jonthomasson/POVSpinner/rev1.c/board_outline/outline5b.dxf

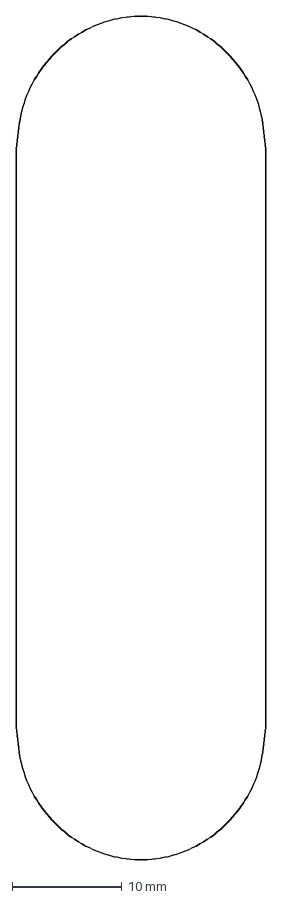
[picture p19: CAD file, 2017-06-09]
rev1.c/board_outline/outline5b.dxf
22.7 x 76.8 mm
