jonthomasson/POVSpinner/rev1.f/3dmodels/Bearings_R188.step

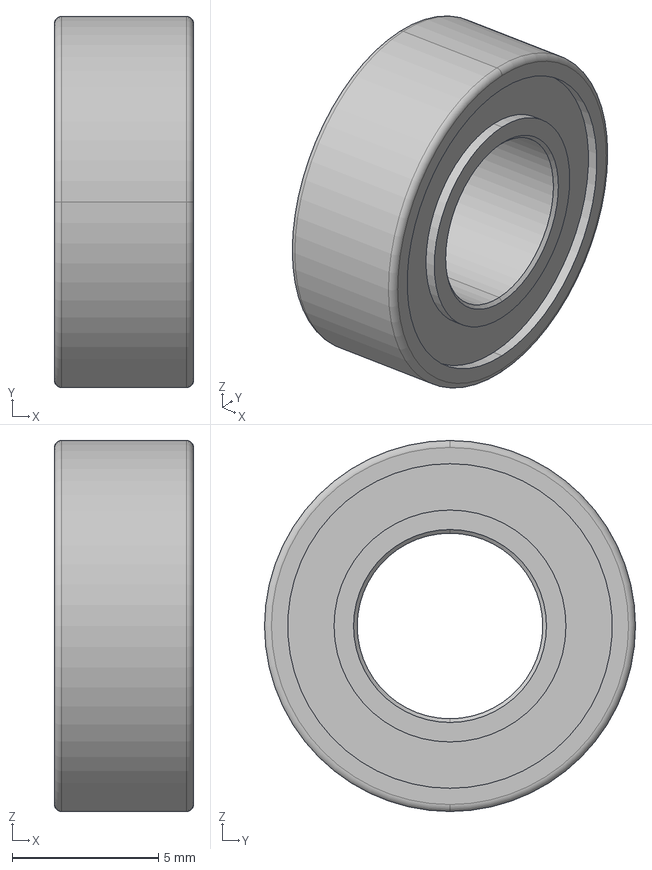
[picture p20: CAD file, 2017-06-09]
rev1.f/3dmodels/Bearings_R188.step
4.76 x 12.7 x 12.7 mm
