jonthomasson/POVSpinner/rev1.f/3dmodels/BK-888.step

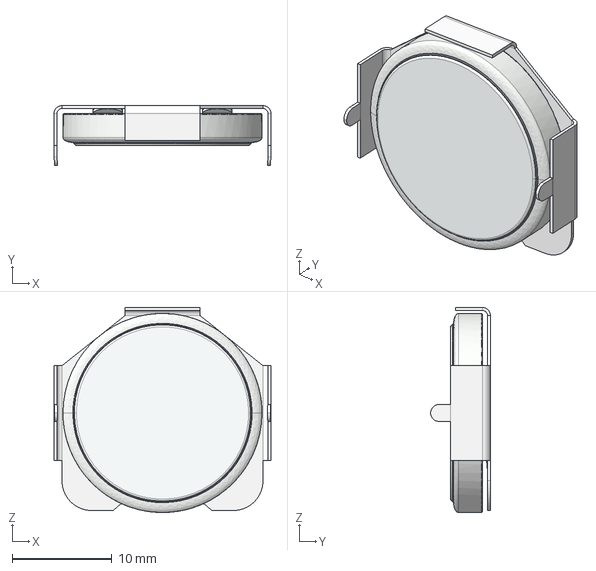
[picture p22: CAD file, 2017-06-09]
rev1.f/3dmodels/BK-888.step
21.8 x 6.01 x 20.6 mm
