jonthomasson/POVSpinner/rev1.c/board_outline/#outline5a.dxf

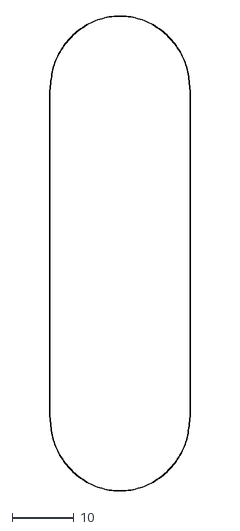
[picture p23: CAD file, 2017-06-09]
rev1.c/board_outline/#outline5a.dxf
22.7 x 76.8
