jonthomasson/POVSpinner/rev1.f/3dmodels/Battery_Holder_MPD_BS_3.step

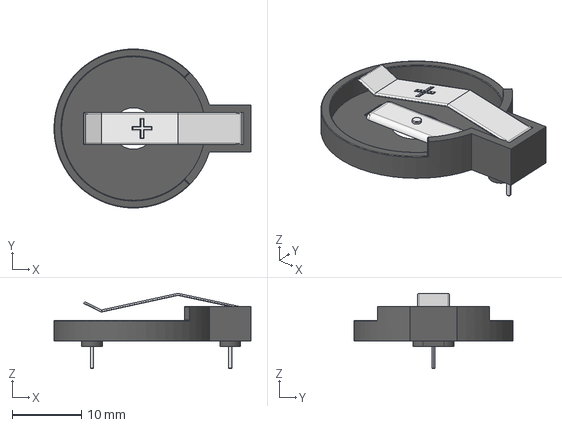
[picture p24: CAD file, 2017-06-09]
rev1.f/3dmodels/Battery_Holder_MPD_BS_3.step
28.5 x 23.0 x 10.9 mm
