jonthomasson/POVSpinner/rev1.f/3dmodels/CL-SB-12B-01T.step

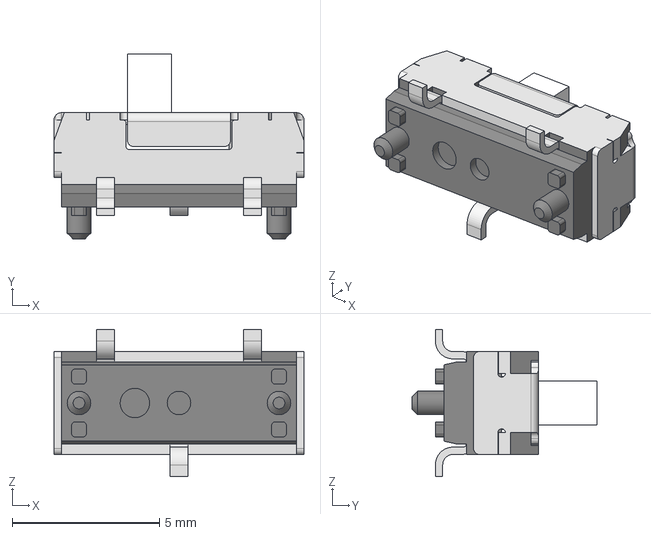
[picture p25: CAD file, 2017-06-09]
rev1.f/3dmodels/CL-SB-12B-01T.step
8.50 x 6.30 x 5.00 mm
