jonthomasson/POVSpinner/rev1.c/board_outline/outline6a.dxf

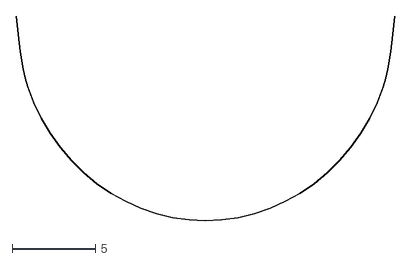
[picture p26: CAD file, 2017-06-09]
rev1.c/board_outline/outline6a.dxf
22.7 x 12.3
