jonthomasson/POVSpinner/rev1.f/3dmodels/PTS810.stp

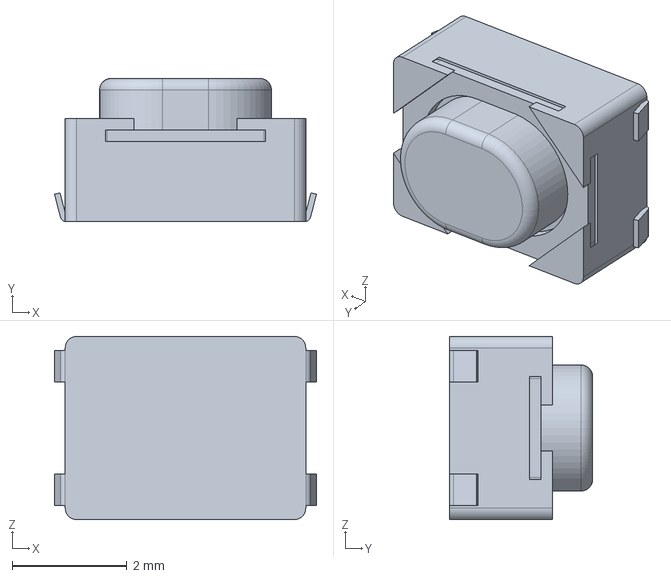
[picture p27: CAD file, 2017-06-09]
rev1.f/3dmodels/PTS810.stp
4.58 x 2.50 x 3.20 mm
