jonthomasson/POVSpinner/rev1.c/board_outline/outline6ab.dxf

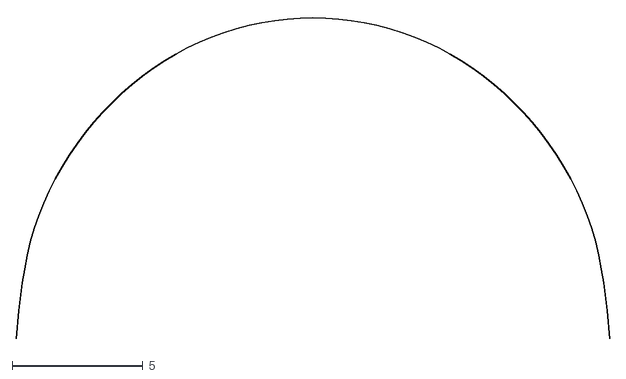
[picture p29: CAD file, 2017-06-09]
rev1.c/board_outline/outline6ab.dxf
22.7 x 12.3
